zapta/legacy_stepper_motor_analyzer/platformio/src/analyzer/quadrants_plot.png

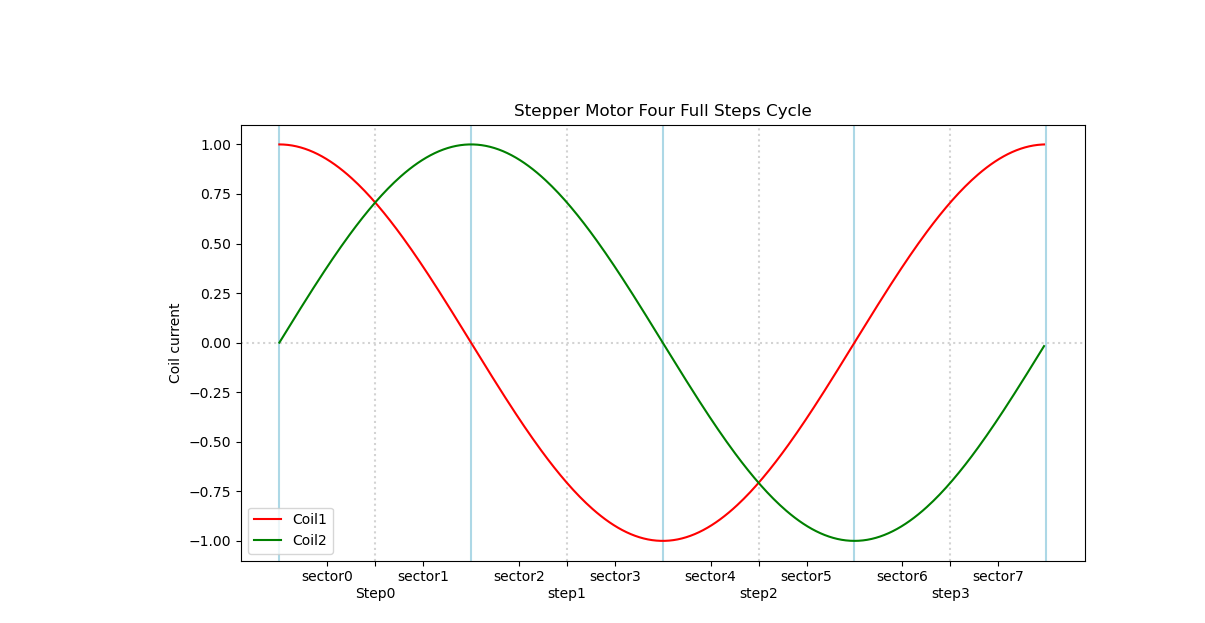
platformio/src/analyzer/quadrants_plot.png
