zapta/legacy_stepper_motor_analyzer/doc/touch/ER-TPC035-6_Drawing.pdf

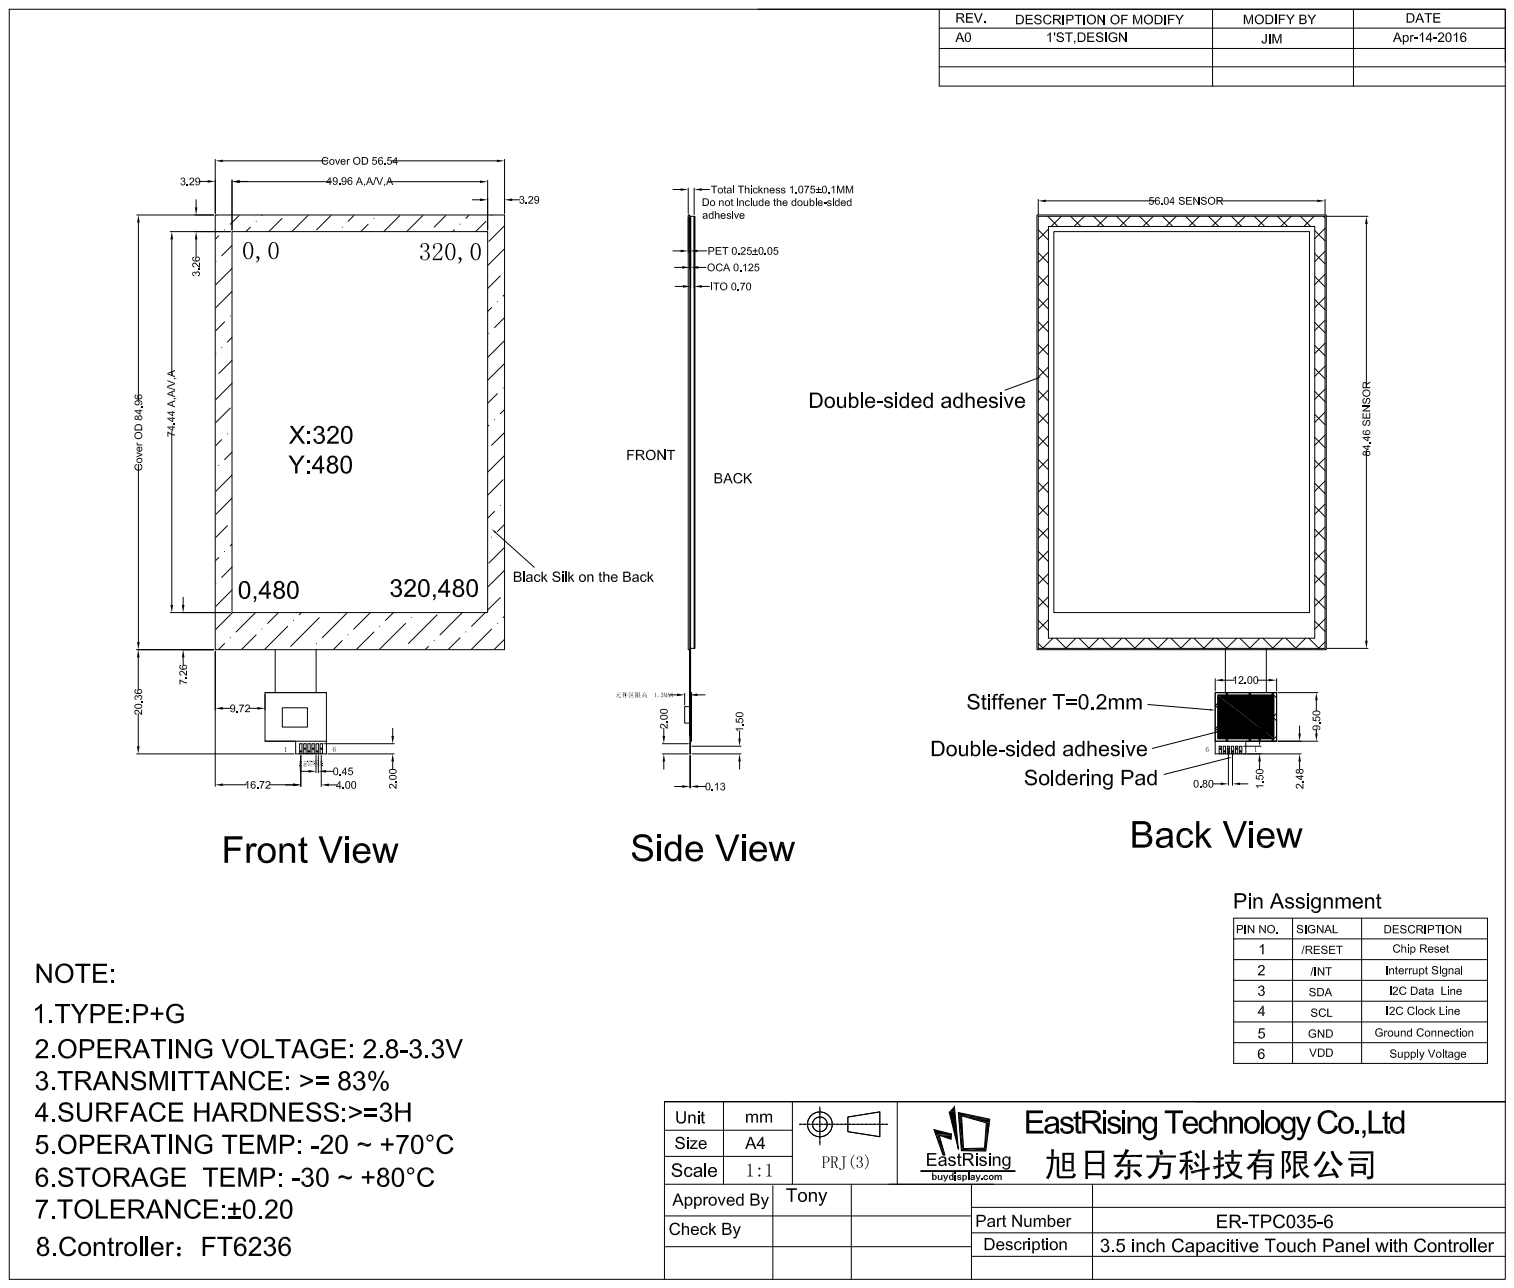
[picture p46: page 1]
