zapta/legacy_stepper_motor_analyzer/platformio/src/hal/adc.cpp

// ADC initialization.

#include "adc.h"

#include "stm32_def.h"

namespace adc {


static void MX_ADC_MspInit(ADC_HandleTypeDef* adcHandle);

ADC_HandleTypeDef hadc1;
DMA_HandleTypeDef hdma_adc1;

void MX_ADC1_Init() {
  ADC_ChannelConfTypeDef sConfig = {0};

  // Common config.
  hadc1.Instance = ADC1;
  hadc1.Init.ClockPrescaler = ADC_CLOCK_SYNC_PCLK_DIV4;
  hadc1.Init.Resolution = ADC_RESOLUTION_12B;
  hadc1.Init.ScanConvMode = ENABLE;
  hadc1.Init.ContinuousConvMode = DISABLE;
  hadc1.Init.DiscontinuousConvMode = DISABLE;
  hadc1.Init.ExternalTrigConvEdge = ADC_EXTERNALTRIGCONVEDGE_RISING;
  hadc1.Init.ExternalTrigConv = ADC_EXTERNALTRIGCONV_T1_CC1;
  hadc1.Init.DataAlign = ADC_DATAALIGN_RIGHT;
  hadc1.Init.NbrOfConversion = 2;
  hadc1.Init.DMAContinuousRequests = ENABLE;
  hadc1.Init.EOCSelection = ADC_EOC_SEQ_CONV;
  if (HAL_ADC_Init(&hadc1) != HAL_OK) {
    Error_Handler();
  }

  /** Configure for the selected ADC regular channel its corresponding rank in
   * the sequencer and its sample time.
   */
  sConfig.Channel = ADC_CHANNEL_8;
  sConfig.Rank = 1;
  sConfig.SamplingTime = ADC_SAMPLETIME_3CYCLES;
  if (HAL_ADC_ConfigChannel(&hadc1, &sConfig) != HAL_OK) {
    Error_Handler();
  }
  /** Configure for the selected ADC regular channel its corresponding rank in
   * the sequencer and its sample time.
   */
  sConfig.Channel = ADC_CHANNEL_9;
  sConfig.Rank = 2;
  if (HAL_ADC_ConfigChannel(&hadc1, &sConfig) != HAL_OK) {
    Error_Handler();
  }

  // TODO: can we let the HAL call this as done with MX Cube generated
  //  code? May need to drop the 'static' and namespace from HAL_ADC_MspInit
  // below.
  MX_ADC_MspInit(&hadc1);
}

// void HAL_ADC_MspInit(ADC_HandleTypeDef* adcHandle) {
static void MX_ADC_MspInit(ADC_HandleTypeDef* adcHandle) {
  GPIO_InitTypeDef GPIO_InitStruct = {0};
  if (adcHandle->Instance == ADC1) {
    /* ADC1 clock enable */
    __HAL_RCC_ADC1_CLK_ENABLE();

    __HAL_RCC_GPIOB_CLK_ENABLE();
    /**ADC1 GPIO Configuration
    PB0     ------> ADC1_IN8
    PB1     ------> ADC1_IN9
    */
    GPIO_InitStruct.Pin = AIN0_Pin | AIN1_Pin;
    GPIO_InitStruct.Mode = GPIO_MODE_ANALOG;
    GPIO_InitStruct.Pull = GPIO_NOPULL;
    HAL_GPIO_Init(GPIOB, &GPIO_InitStruct);

    /* ADC1 DMA Init */
    /* ADC1 Init */
    hdma_adc1.Instance = DMA2_Stream0;
    hdma_adc1.Init.Channel = DMA_CHANNEL_0;
    hdma_adc1.Init.Direction = DMA_PERIPH_TO_MEMORY;
    hdma_adc1.Init.PeriphInc = DMA_PINC_DISABLE;
    hdma_adc1.Init.MemInc = DMA_MINC_ENABLE;
    hdma_adc1.Init.PeriphDataAlignment = DMA_PDATAALIGN_HALFWORD;
    hdma_adc1.Init.MemDataAlignment = DMA_MDATAALIGN_HALFWORD;
    hdma_adc1.Init.Mode = DMA_CIRCULAR;
    hdma_adc1.Init.Priority = DMA_PRIORITY_LOW;
    hdma_adc1.Init.FIFOMode = DMA_FIFOMODE_ENABLE;
    hdma_adc1.Init.FIFOThreshold = DMA_FIFO_THRESHOLD_HALFFULL;
    hdma_adc1.Init.MemBurst = DMA_MBURST_SINGLE;
    hdma_adc1.Init.PeriphBurst = DMA_PBURST_SINGLE;
    if (HAL_DMA_Init(&hdma_adc1) != HAL_OK) {
      Error_Handler();
    }

    __HAL_LINKDMA(adcHandle, DMA_Handle, hdma_adc1);

  }
}

}  // namespace adc
