zapta/legacy_stepper_motor_analyzer/platformio/src/display/bssr_tables.h

// Lookup tables to drive the 16 bits parallel output.
#pragma once

#include <Arduino.h>

namespace bssr_tables {

extern const uint64_t direct_bssr_table[];
extern const uint64_t color_bssr_table[];

}  // namespace bssr_tables
